YashasSingh/GAMEBOARD/img/c.png

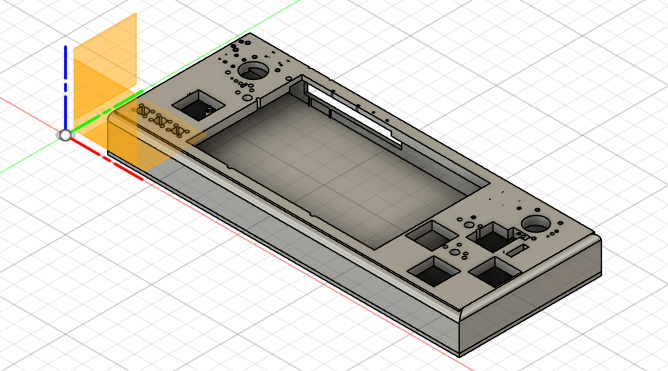
img/c.png
