YashasSingh/GAMEBOARD/img/r.png

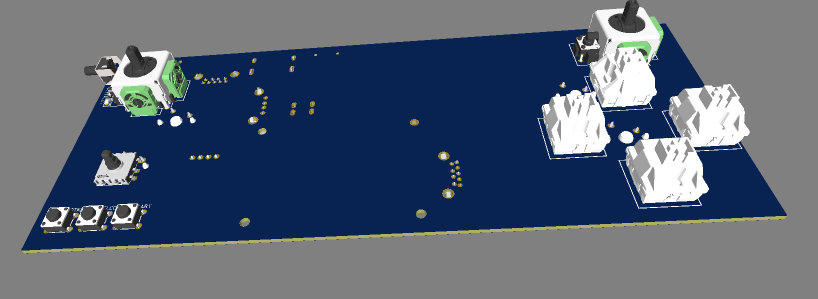
img/r.png
